whitenhiemer/cyberdeck/photos/20260506_140017.jpg

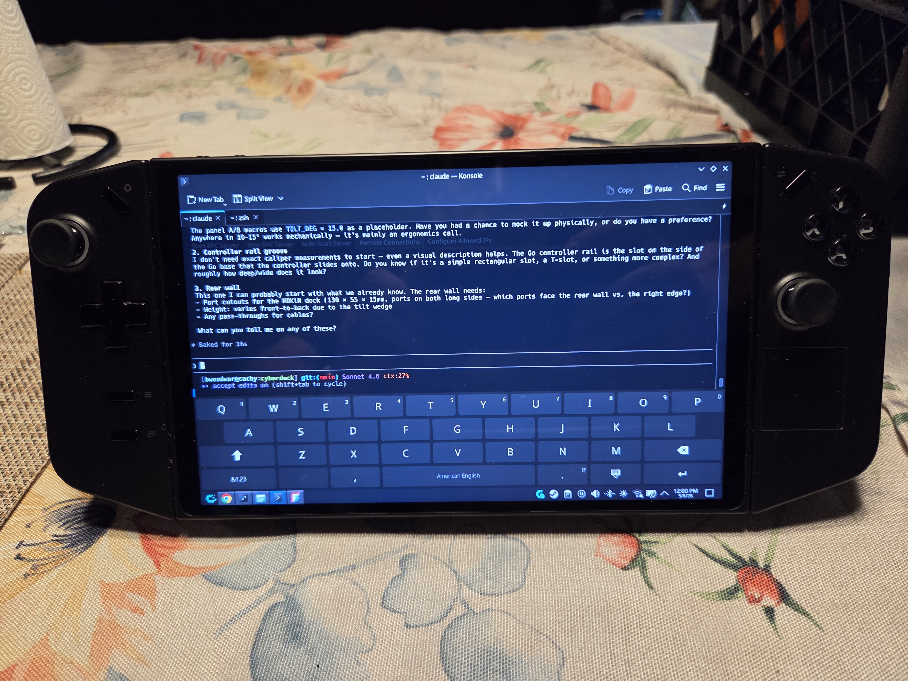
photos/20260506_140017.jpg
