whitenhiemer/cyberdeck/photos/20260506_140027.jpg

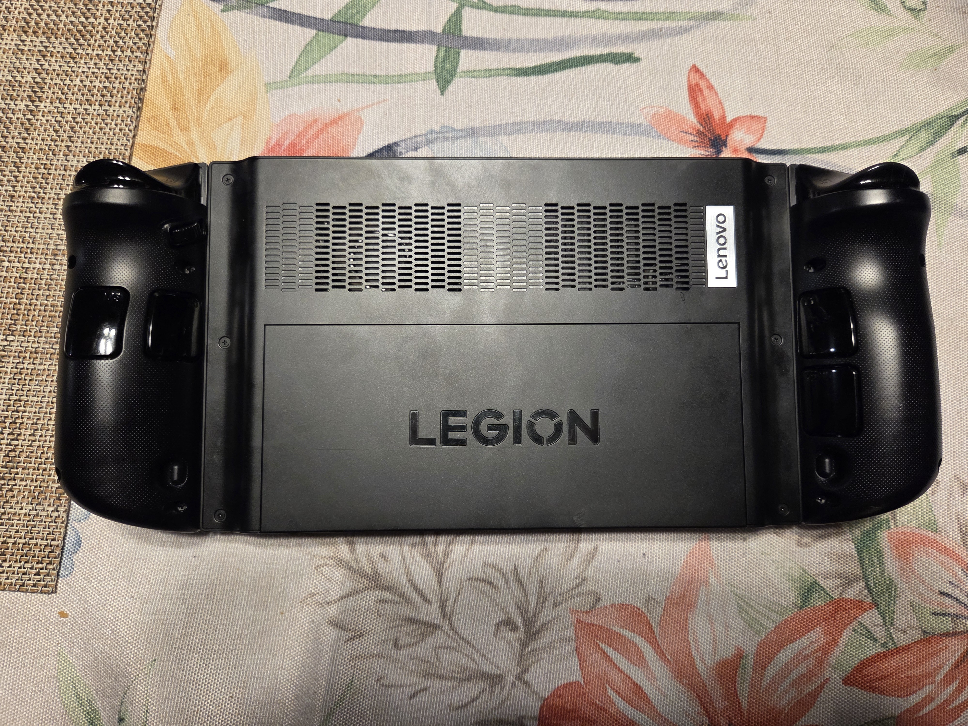
photos/20260506_140027.jpg
