whitenhiemer/cyberdeck/photos/20260506_140037.jpg

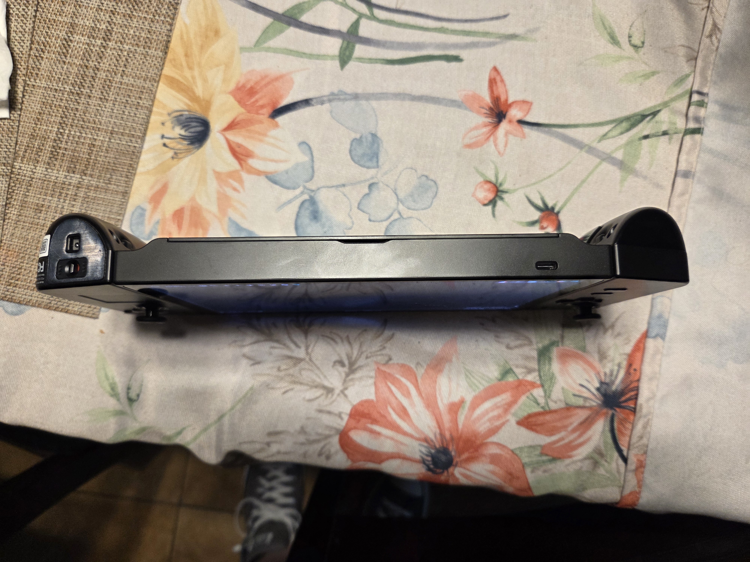
photos/20260506_140037.jpg
