whitenhiemer/cyberdeck/photos/20260506_140052.jpg

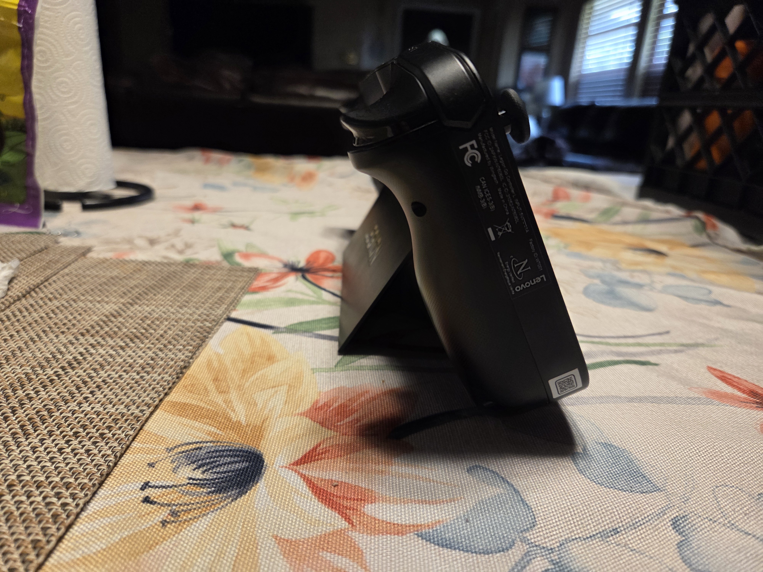
photos/20260506_140052.jpg
