whitenhiemer/cyberdeck/photos/20260506_140109.jpg

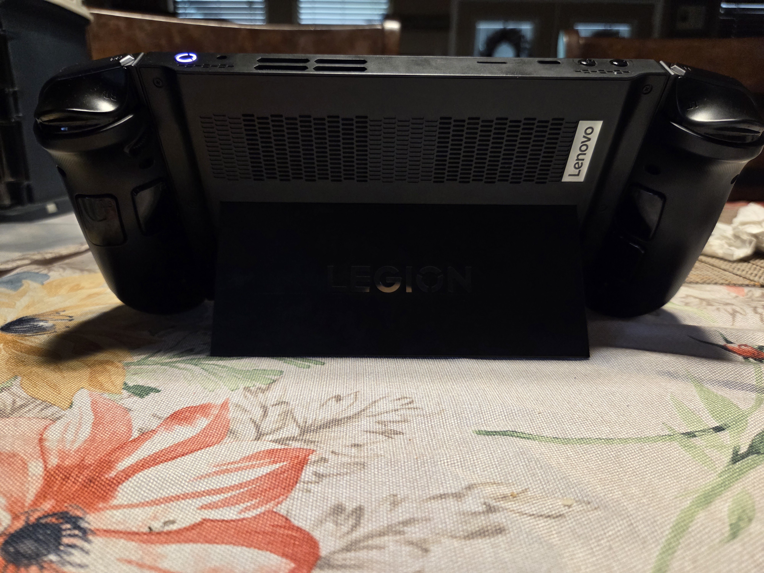
photos/20260506_140109.jpg
