whitenhiemer/cyberdeck/photos/20260506_140814.jpg

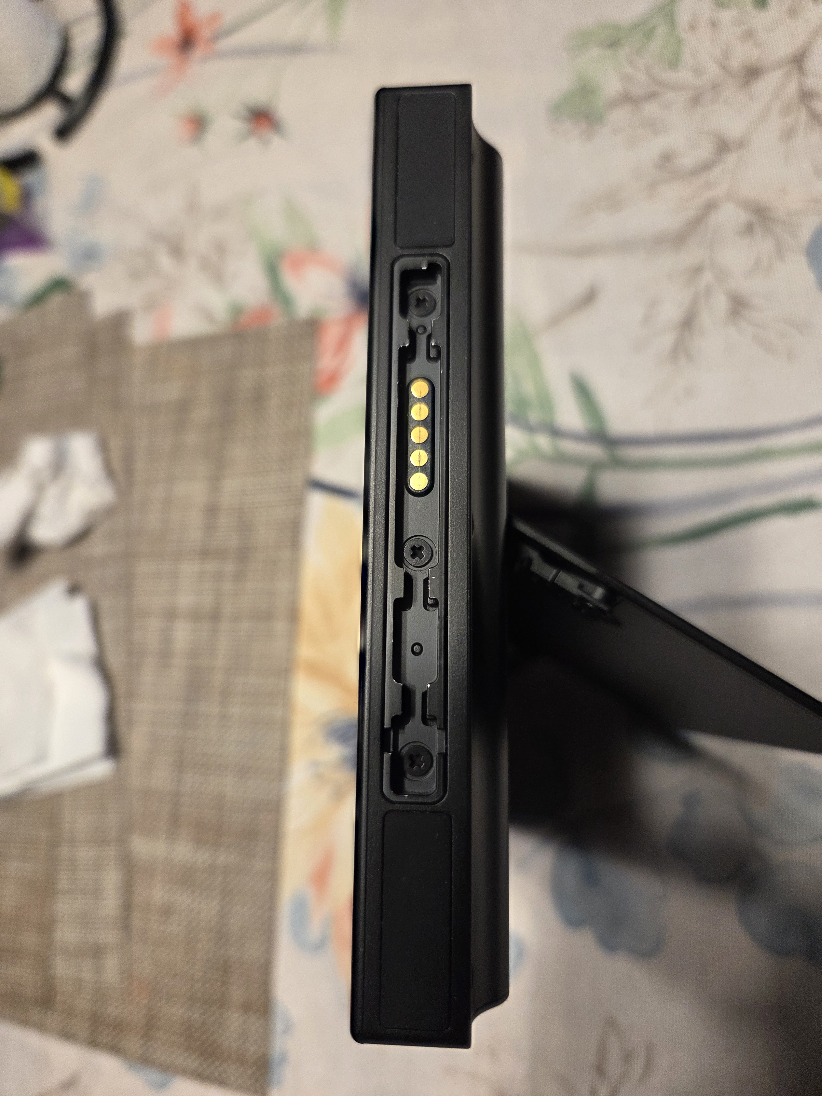
photos/20260506_140814.jpg
