whitenhiemer/cyberdeck/photos/20260506_140822.jpg

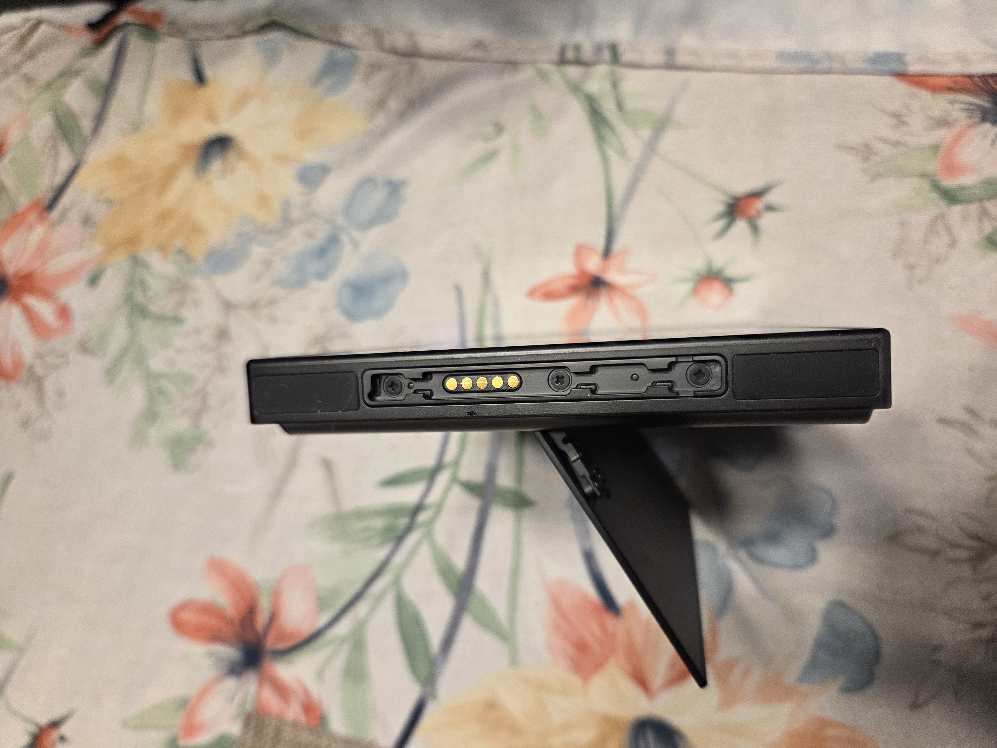
photos/20260506_140822.jpg
